marc15776/Heltec_V4_Adapter/Original_Repo_kiu/pics/lofence_mass_assembly.jpg

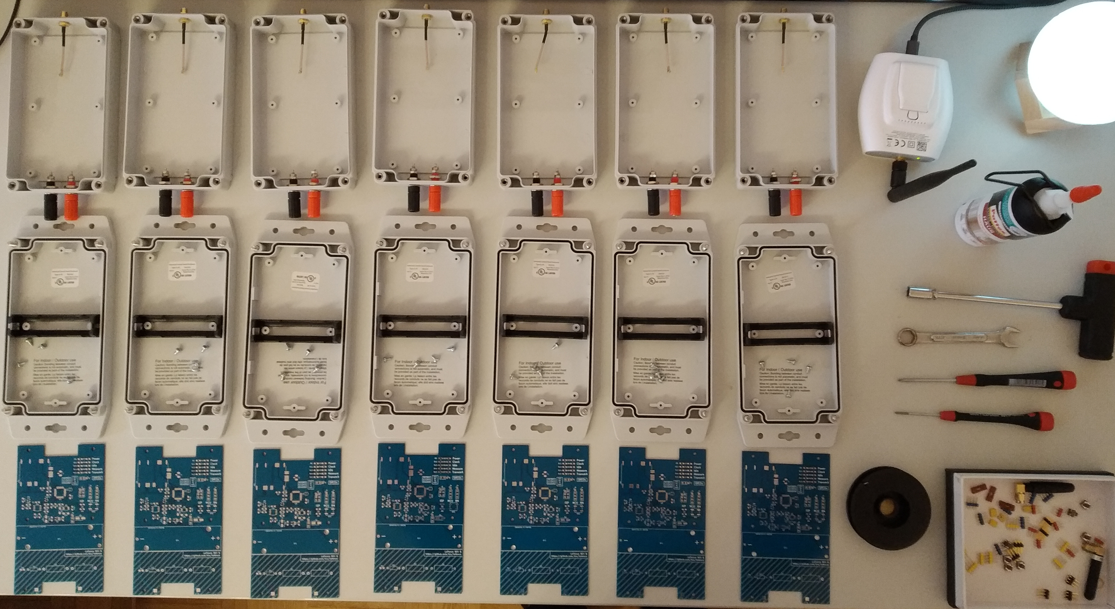
Original_Repo_kiu/pics/lofence_mass_assembly.jpg
