marc15776/Heltec_V4_Adapter/Original_Repo_kiu/pics/lofence_grafana_details.png

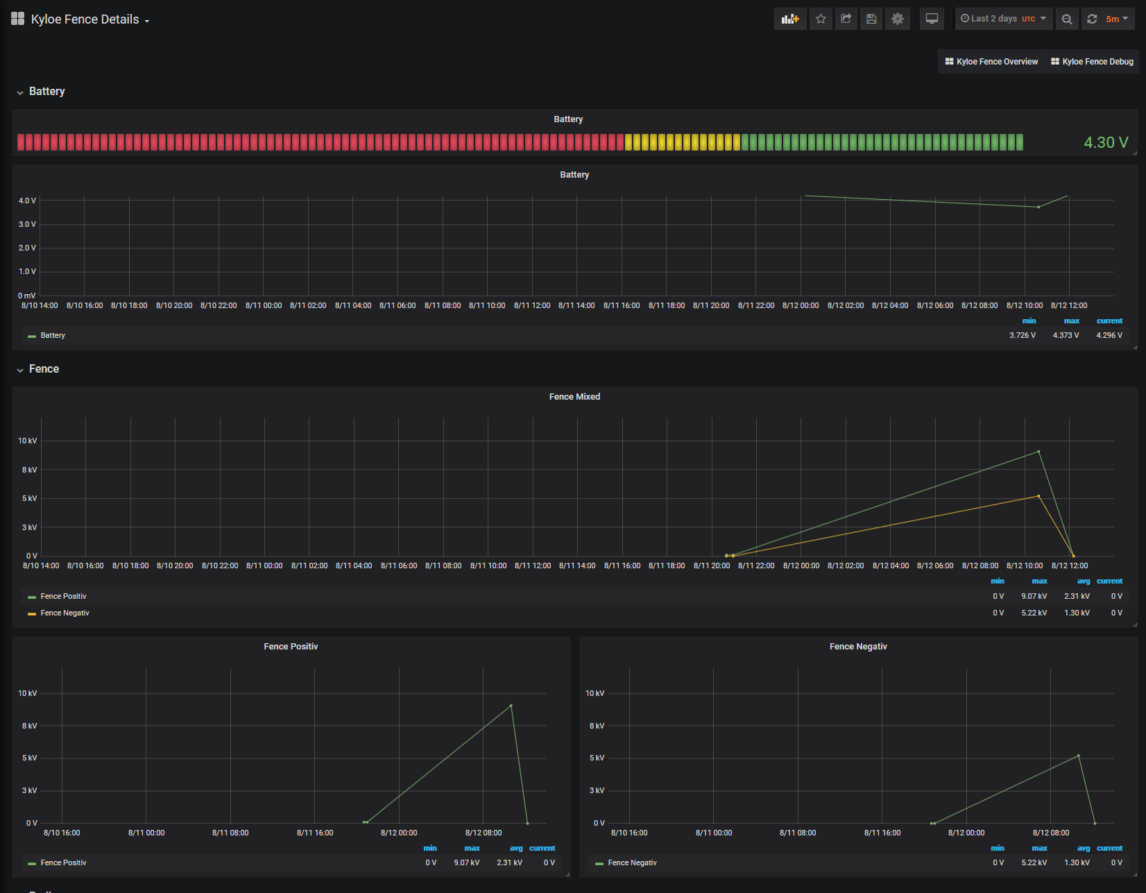
Original_Repo_kiu/pics/lofence_grafana_details.png
