marc15776/Heltec_V4_Adapter/Original_Repo_kiu/pics/lofence_reva_proto.jpg

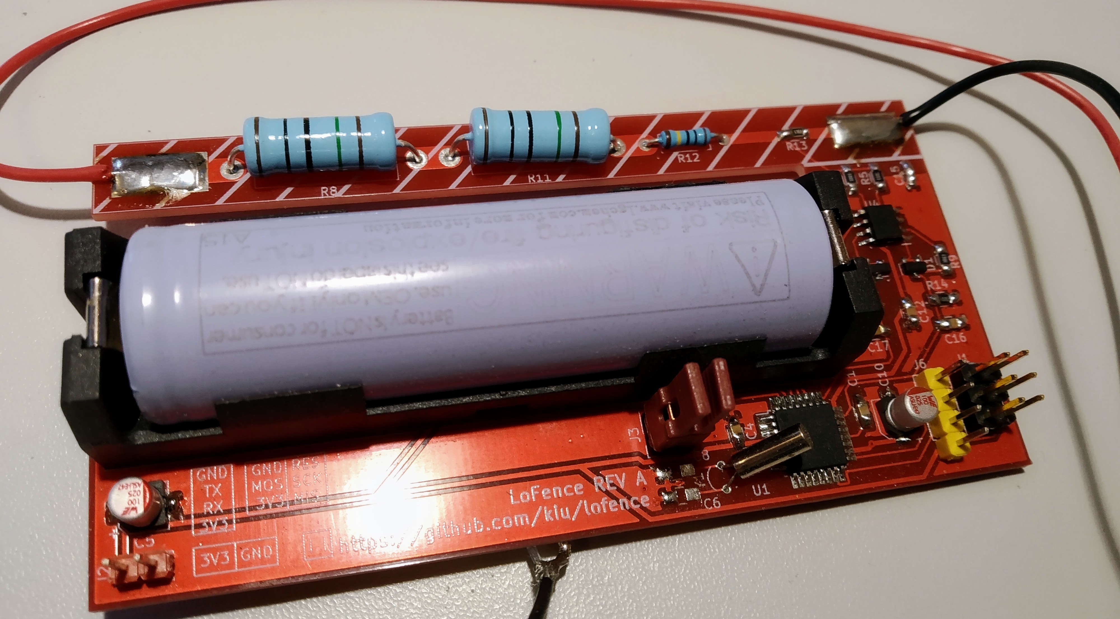
Original_Repo_kiu/pics/lofence_reva_proto.jpg
