marc15776/Heltec_V4_Adapter/Original_Repo_kiu/pics/lofence_revb_final_thumb.jpg

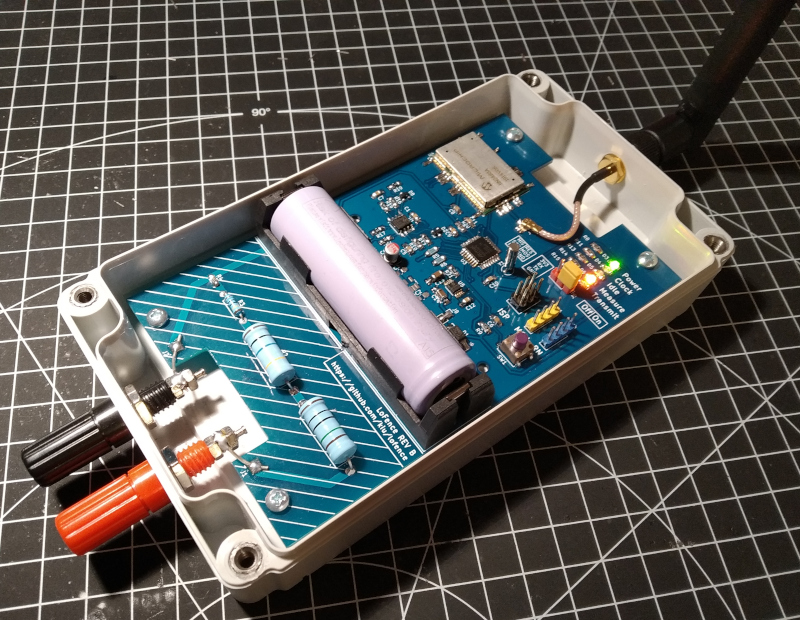
Original_Repo_kiu/pics/lofence_revb_final_thumb.jpg
