marc15776/Heltec_V4_Adapter/Original_Repo_kiu/pics/lofence_rfm95_proto.jpg

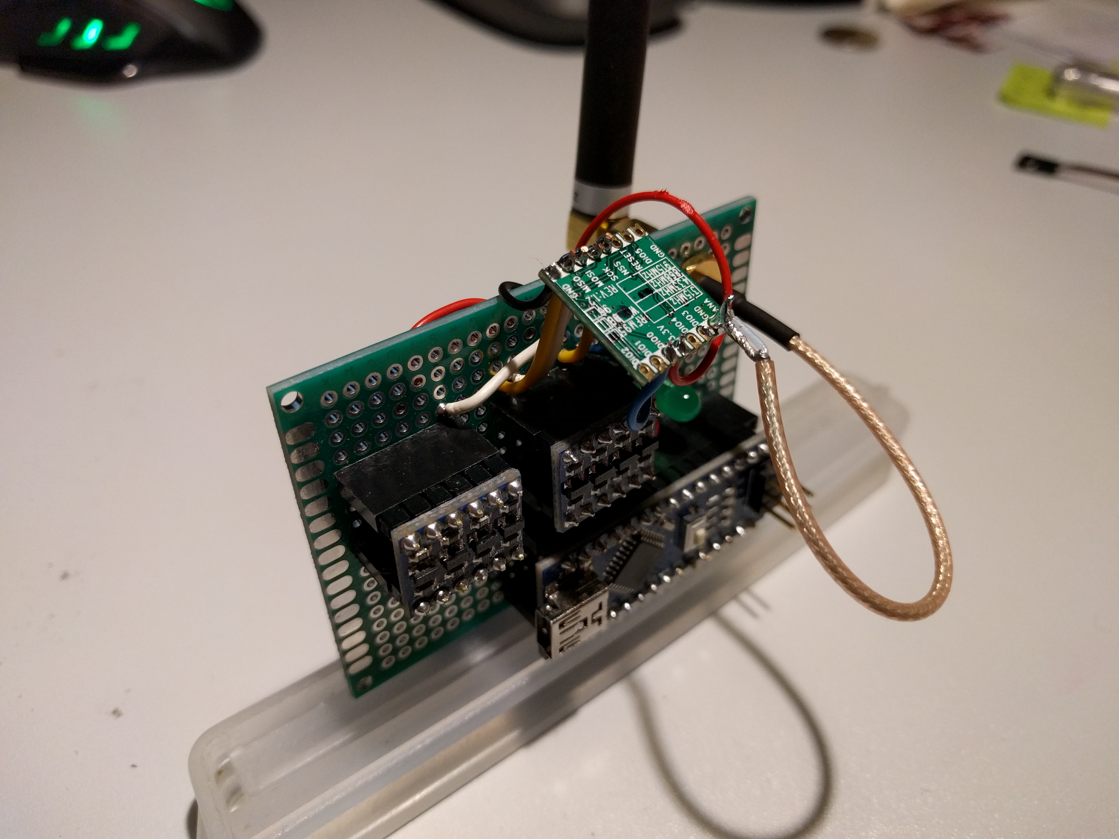
Original_Repo_kiu/pics/lofence_rfm95_proto.jpg
