marc15776/Heltec_V4_Adapter/Original_Repo_kiu/pics/lofence_ttig.jpg

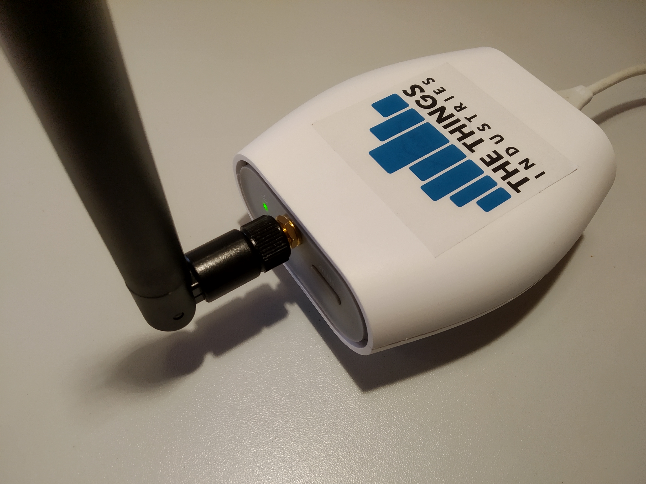
Original_Repo_kiu/pics/lofence_ttig.jpg
