marc15776/Heltec_V4_Adapter/Original_Repo_kiu/pics/lofence_ttn_decoder.png

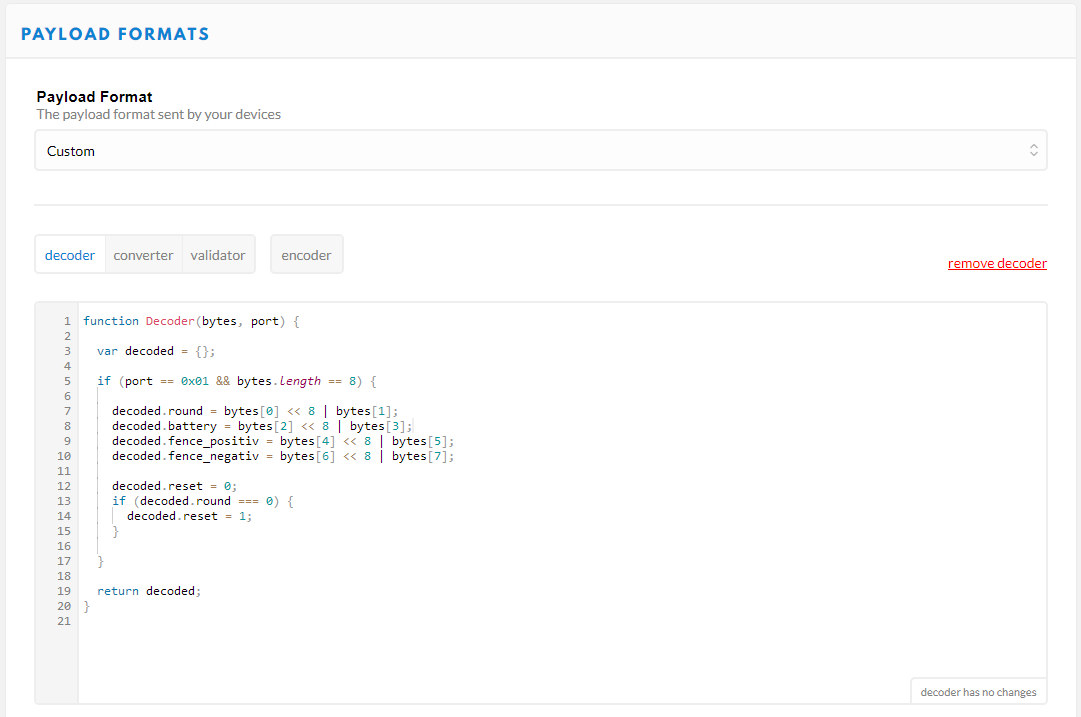
Original_Repo_kiu/pics/lofence_ttn_decoder.png
