marc15776/Heltec_V4_Adapter/Original_Repo_kiu/rev_b/hardware/kicad_lofence_render_front.png

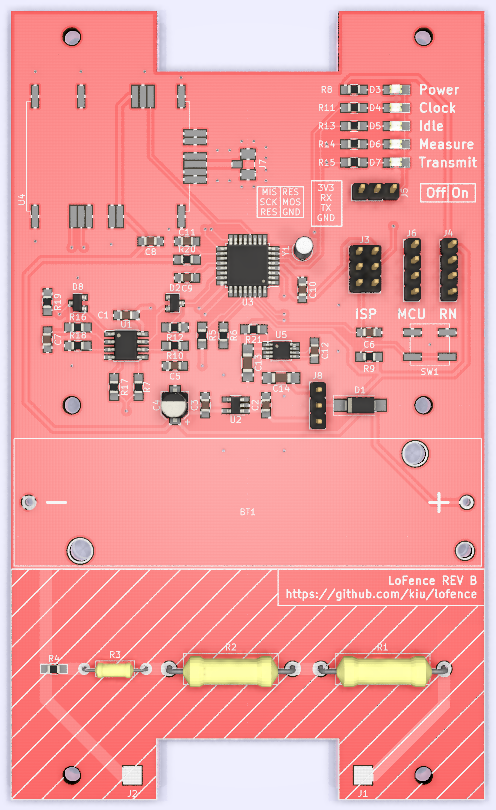
Original_Repo_kiu/rev_b/hardware/kicad_lofence_render_front.png
